MOSH-Insa-Toulouse/2023-2024-4GP-AMODE-GUNDAY/LTSPICE/test.asc

C1: cap; 100p
R1: res; 10k
V1: voltage; PULSE(0 1 10u 1u 1u 10u 0 2); AC 1
Named nets: 0, out
;tran 100u
.ac dec 100 1 0.1G
