MOSH-Insa-Toulouse/2023-2024-4GP-AMODE-GUNDAY/LTSPICE/capteur.asc

C1: cap; 100n
C2: cap; 1µ
C3: cap; 100n
R1: res; 100k
R2: res; 1k
R3: res; 100k
R4: res; 1k
R5: res; 10k
U1: LTC1050
V1: voltage; 5
V2: voltage; SINE(0 1 0.2 0.1 10); AC 1
X1: GP_Capteur_Graphite
Named nets: 0, ADC
;tran 0 10u 0
.ac oct 200 0.1 0.1G
.param G0 10n
.param R0 1k
.param C0 200p
